tom-spi/NMEA-0183-Optical-Link/Schematics+PCB (PDFs)/7. Tx_PCB_Mech.pdf

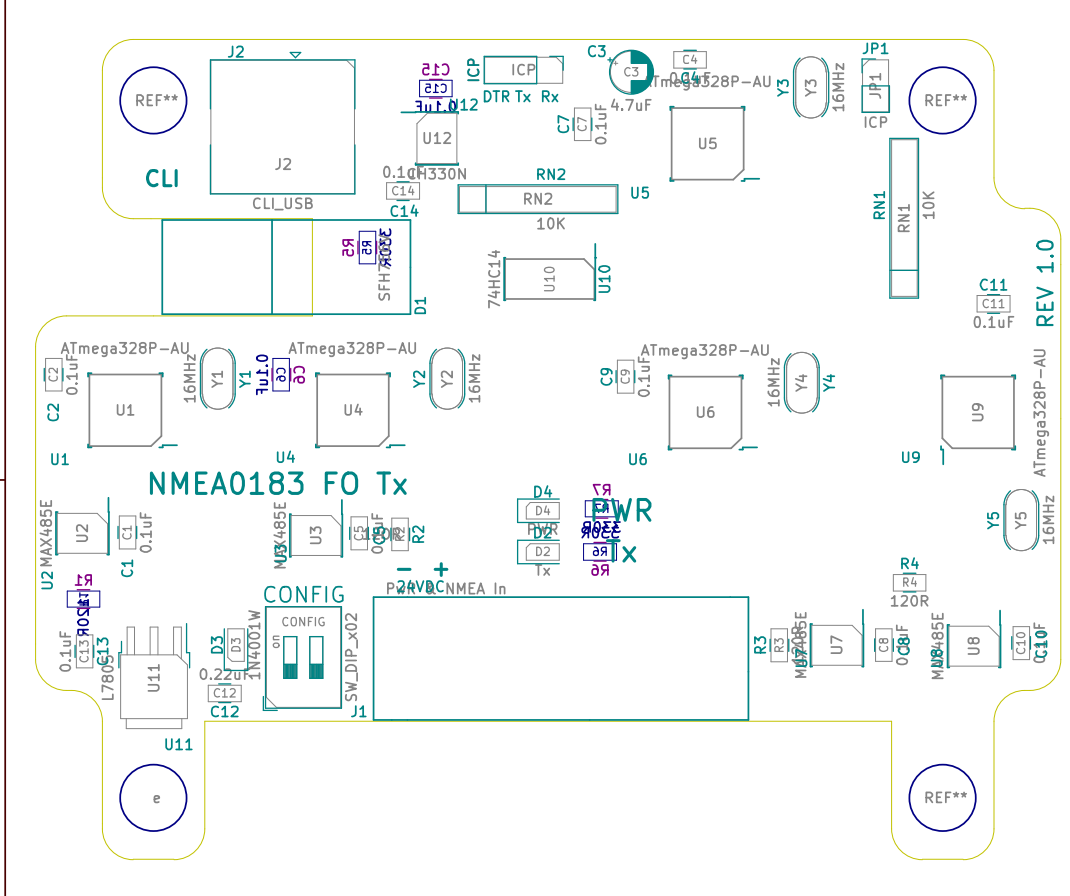
[picture p13: page 1]
