tom-spi/NMEA-0183-Optical-Link/Schematics+PCB (PDFs)/8. Rx_PCBV1.1_allLayers.pdf

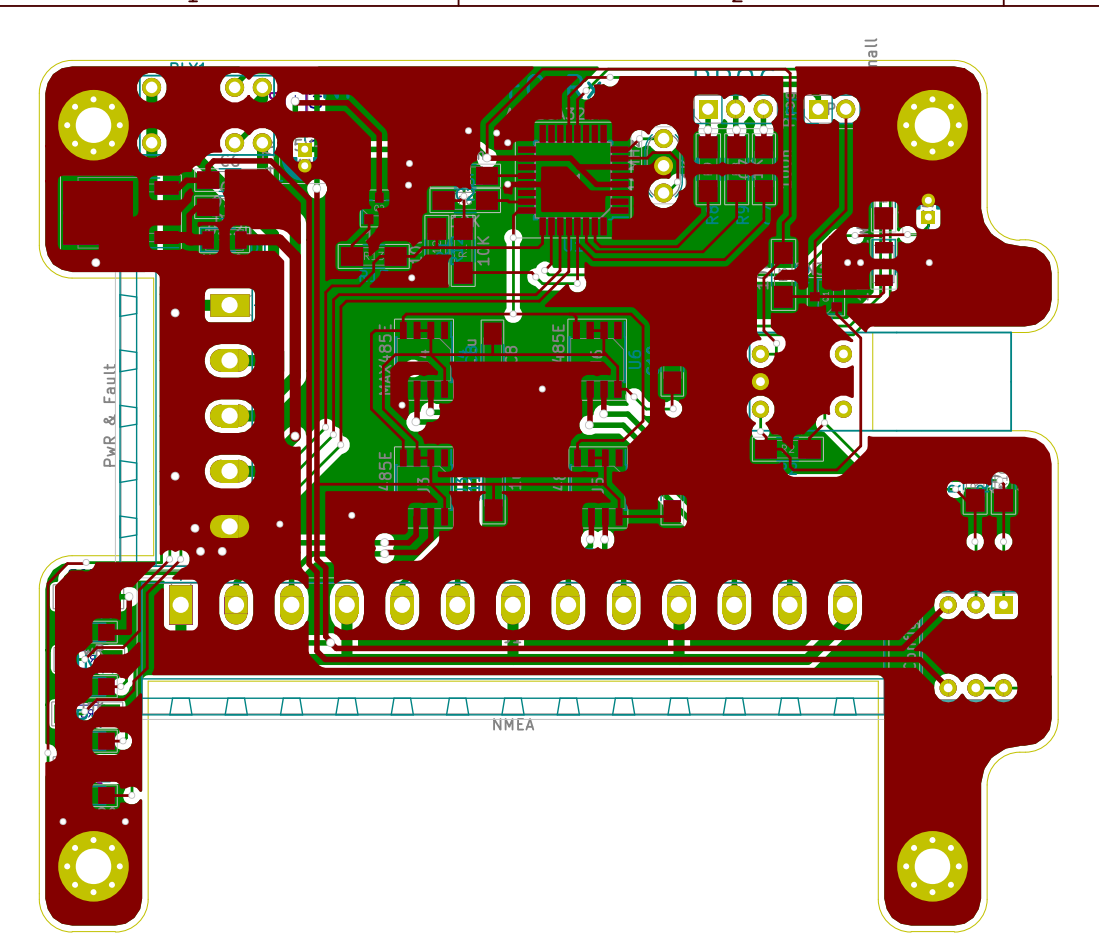
[picture p14: page 1]
