tom-spi/NMEA-0183-Optical-Link/Schematics+PCB (PDFs)/9. Rx_PCBV1.1_Fcu.pdf

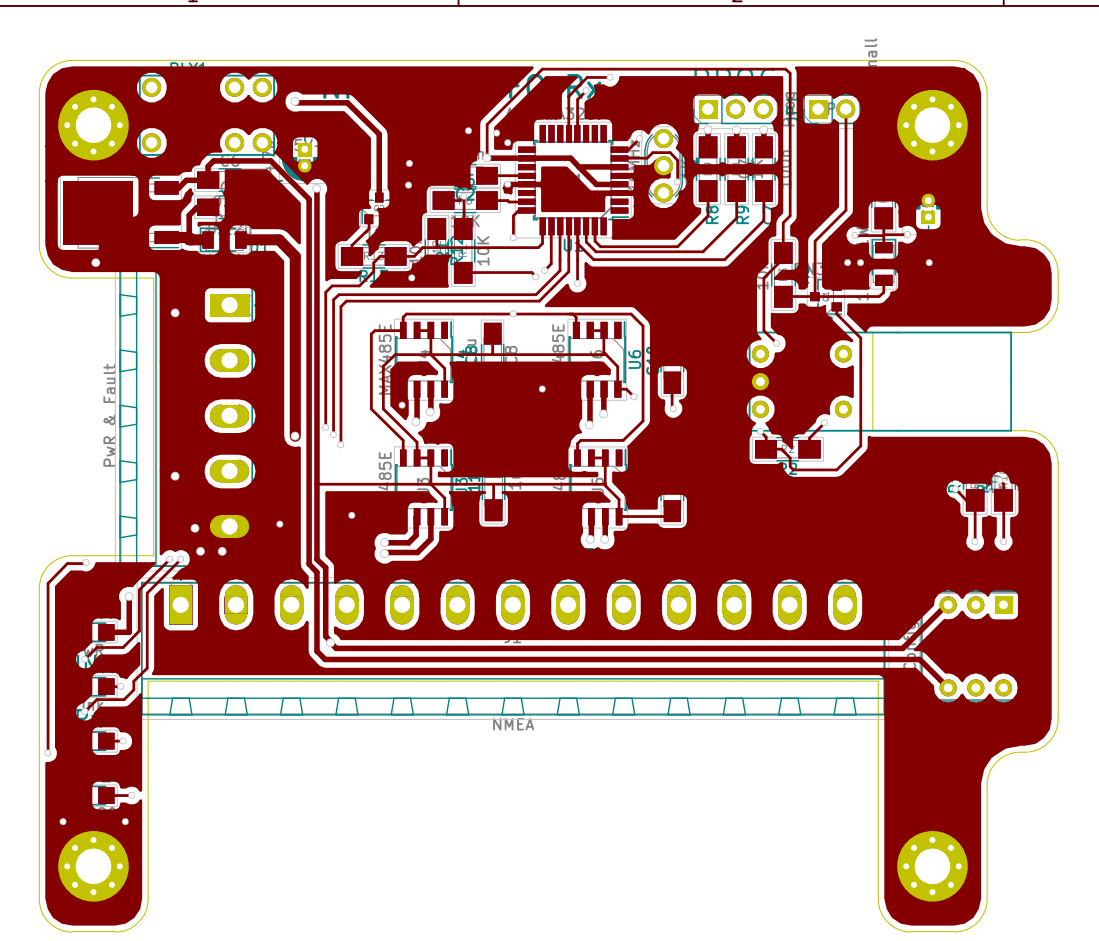
[picture p15: page 1]
